IgorCattusso/keyboards/Nexus-58-Mk-I/photos/Right Side - Full View.jpeg

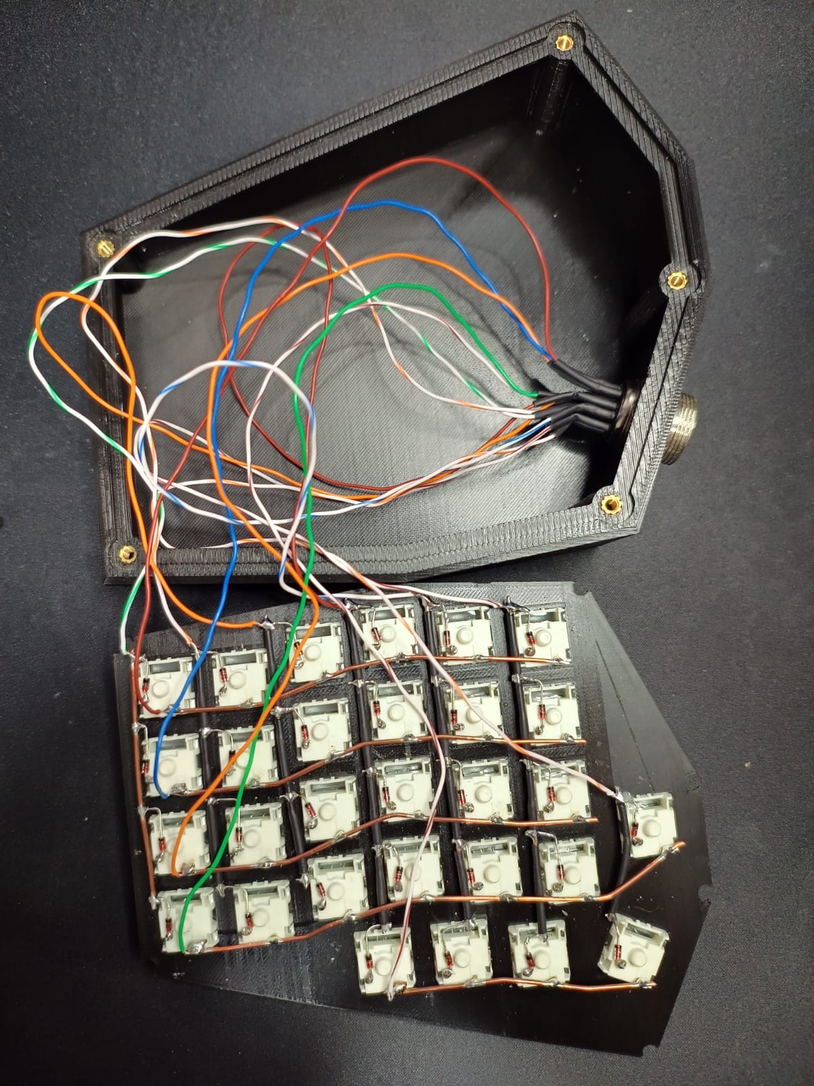
Nexus-58-Mk-I/photos/Right Side - Full View.jpeg
