IgorCattusso/keyboards/Nexus-58-Mk-I/photos/Right Side - Switches Wiring.jpeg

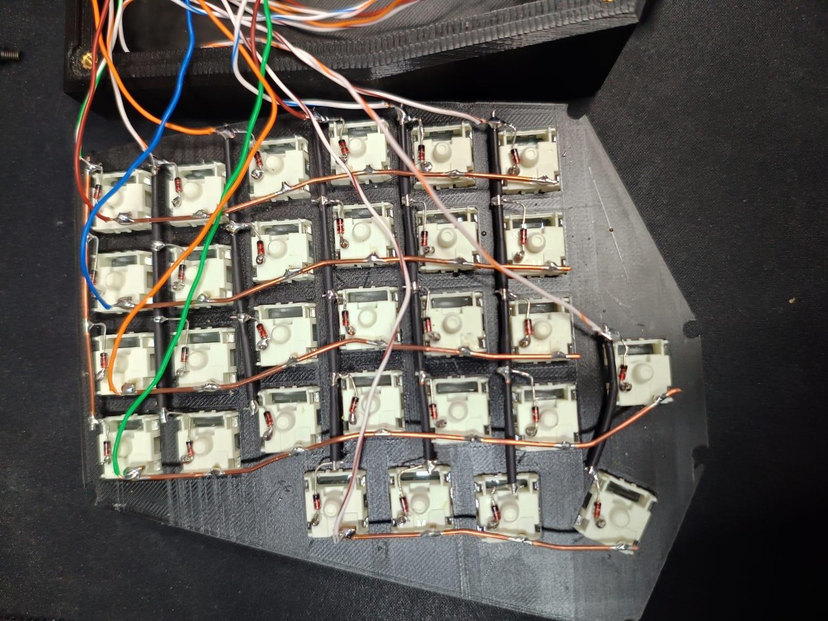
Nexus-58-Mk-I/photos/Right Side - Switches Wiring.jpeg
